hemantghuge/BE_AGV_Project/nodeMCU/esp8266_web_server_13_Feb_20/data/agv.png

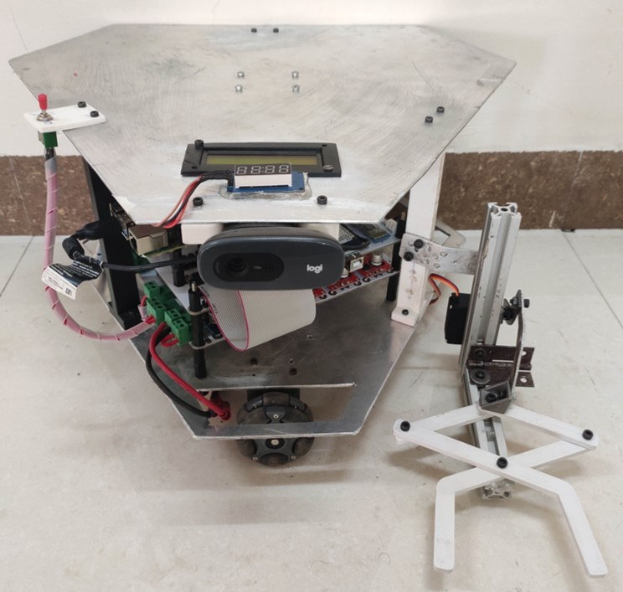
nodeMCU/esp8266_web_server_13_Feb_20/data/agv.png
